Danjovic/TicTacX/doc/boardVersions16F648A.png

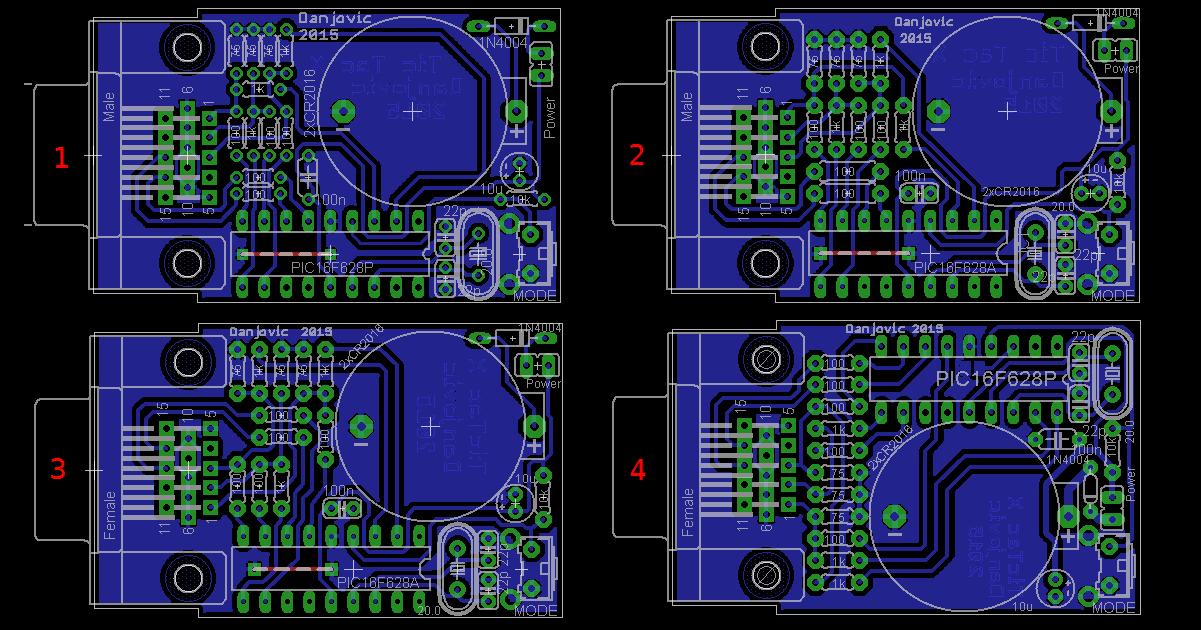
doc/boardVersions16F648A.png
