Danjovic/TicTacX/doc/boardVersions16F688.png

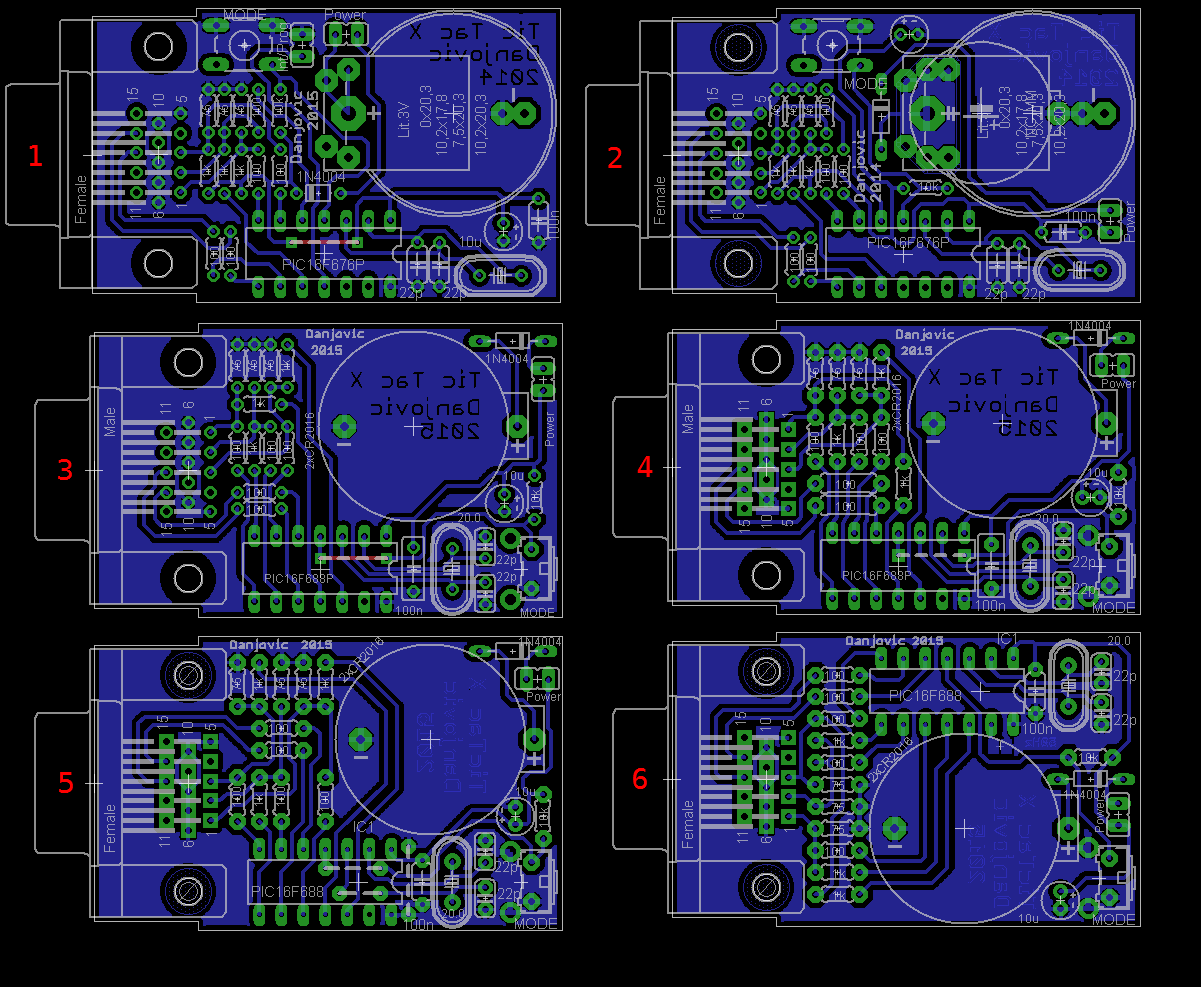
doc/boardVersions16F688.png
