Danjovic/TicTacX/doc/modos.png

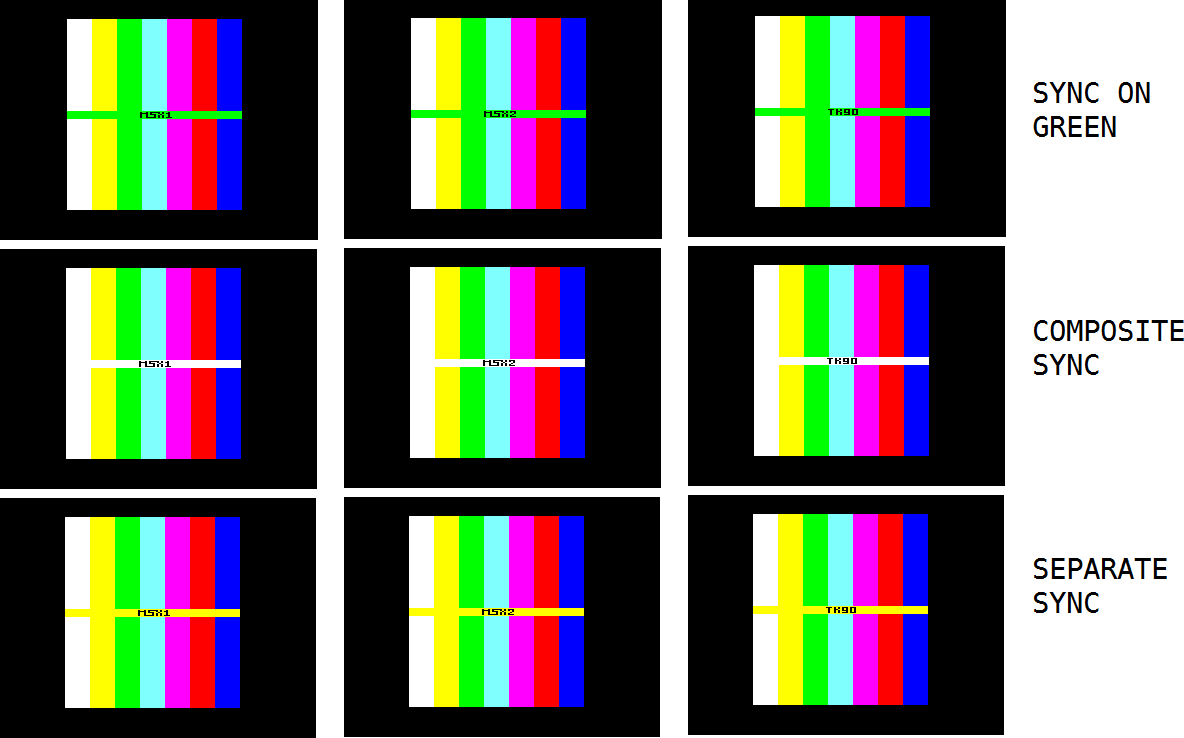
doc/modos.png
