Danjovic/TicTacX/doc/NEC-EA192M/DSC_2613.jpg

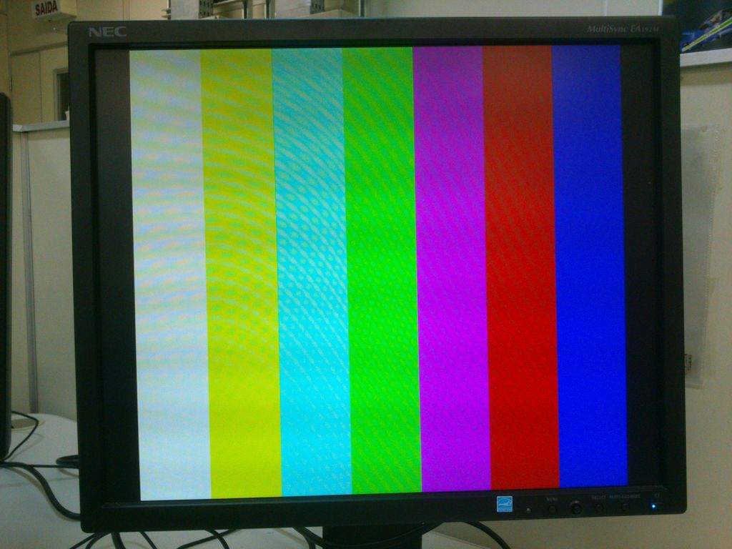
doc/NEC-EA192M/DSC_2613.jpg
