Danjovic/TicTacX/doc/NEC-EA192M/DSC_2616.jpg

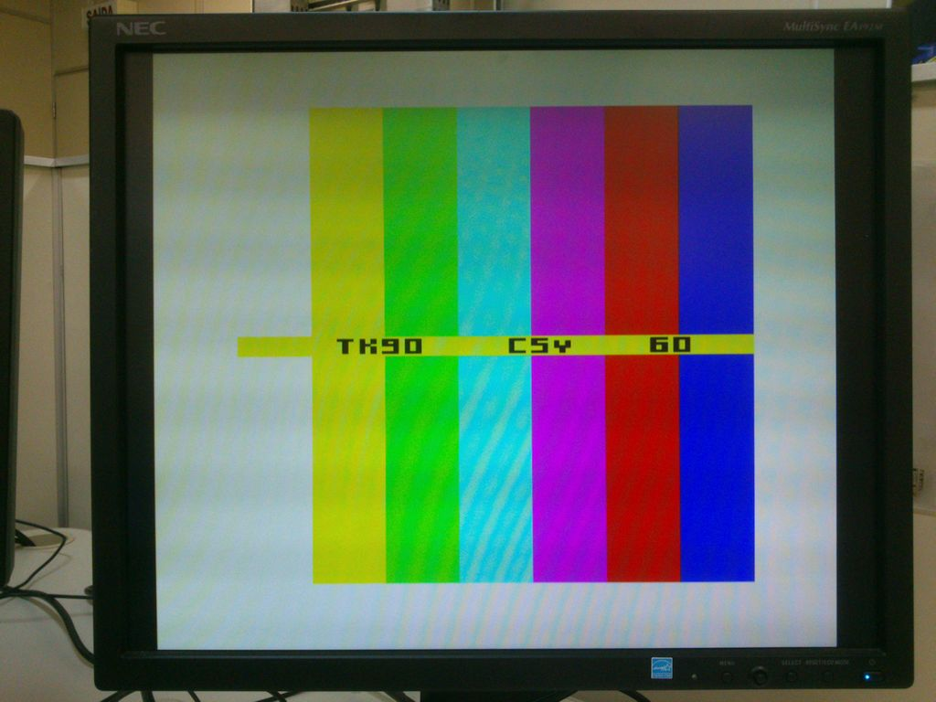
doc/NEC-EA192M/DSC_2616.jpg
