Danjovic/TicTacX/doc/NEC-EA192M/DSC_2620.jpg

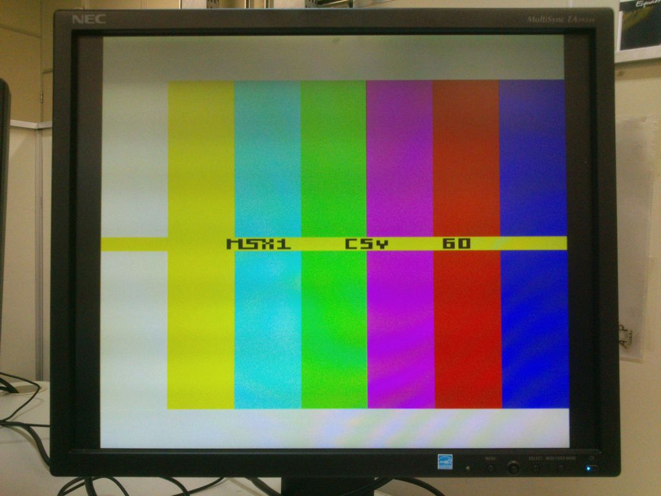
doc/NEC-EA192M/DSC_2620.jpg
