Danjovic/TicTacX/doc/NEC-EA192M/DSC_2622.jpg

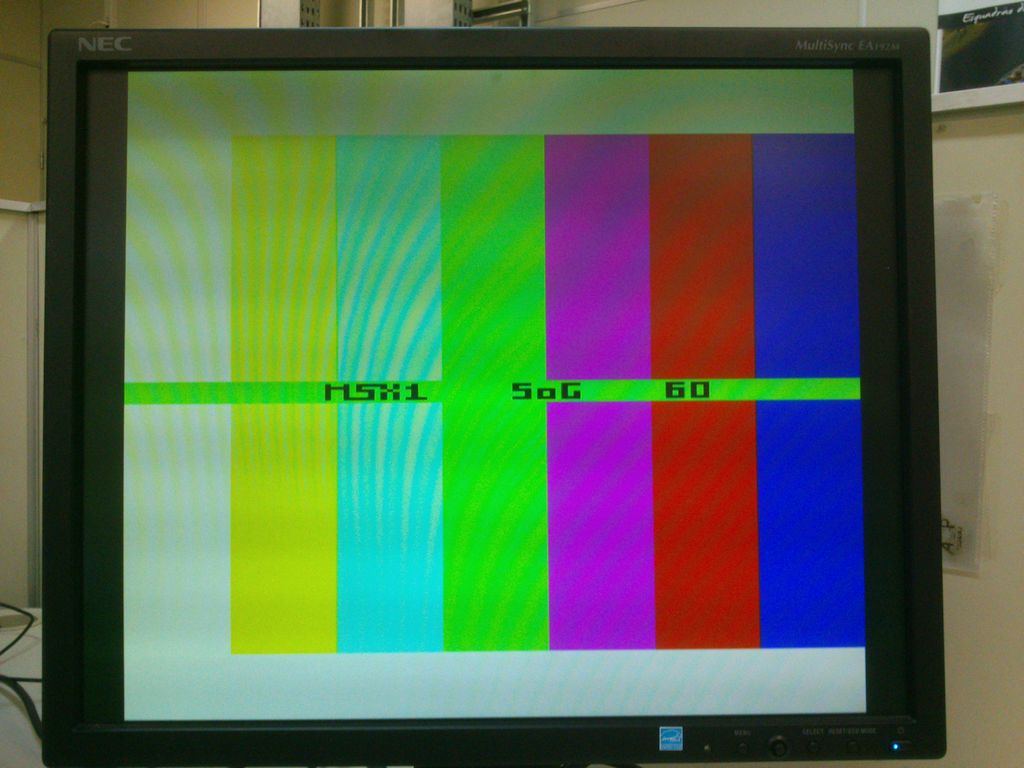
doc/NEC-EA192M/DSC_2622.jpg
