Danjovic/TicTacX/doc/NEC-EA192M/DSC_2623.jpg

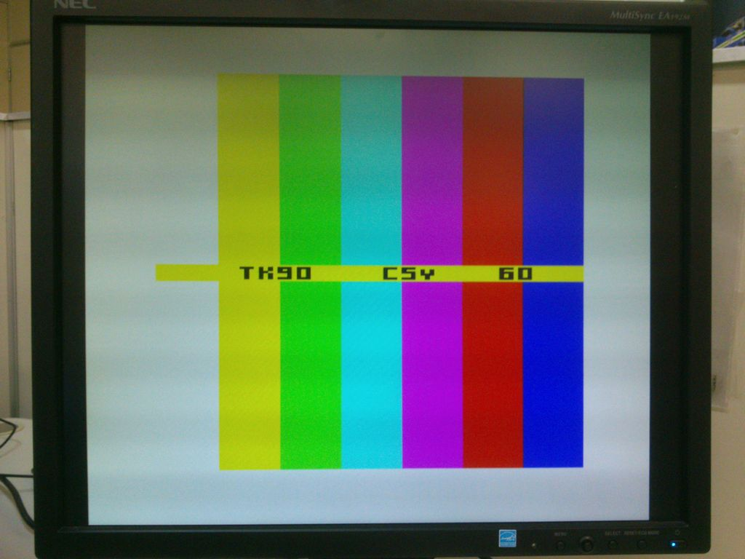
doc/NEC-EA192M/DSC_2623.jpg
