Danjovic/TicTacX/doc/NEC-EA192M/DSC_2625.jpg

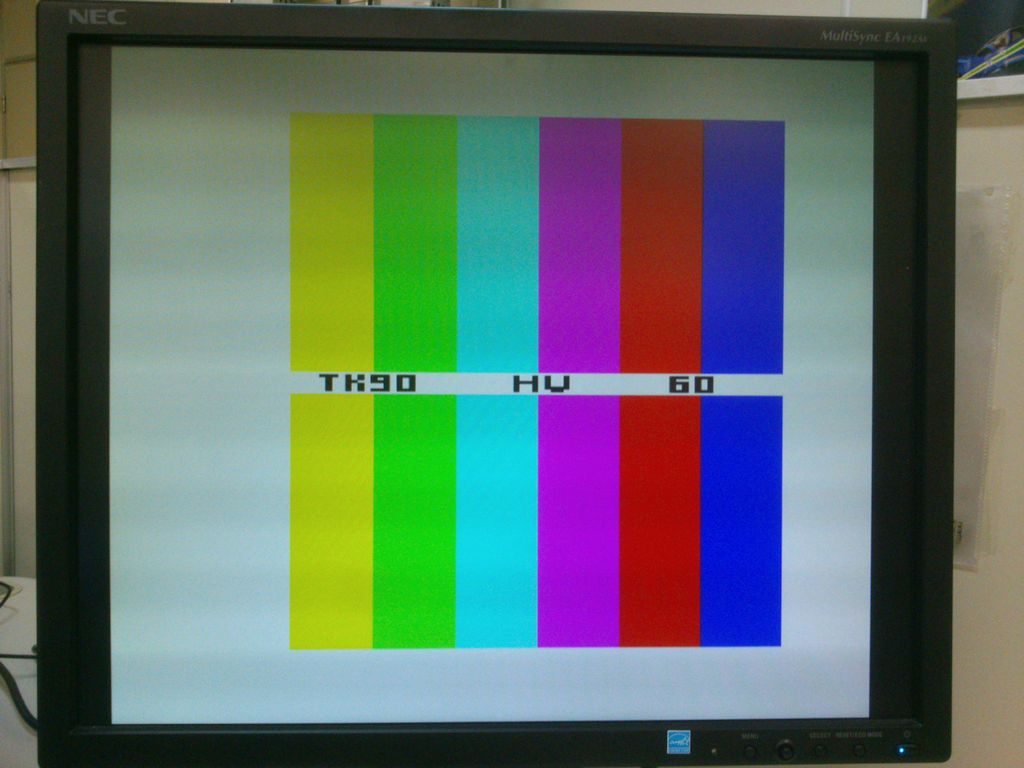
doc/NEC-EA192M/DSC_2625.jpg
