Danjovic/TicTacX/doc/NEC-EA192M/DSC_2626.jpg

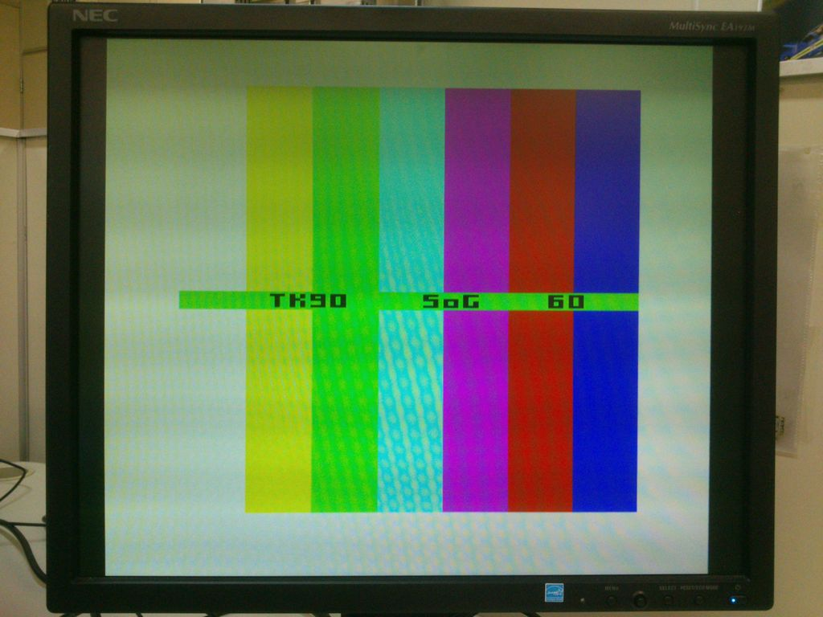
doc/NEC-EA192M/DSC_2626.jpg
