Danjovic/TicTacX/doc/NEC-EA192M/DSC_2627.jpg

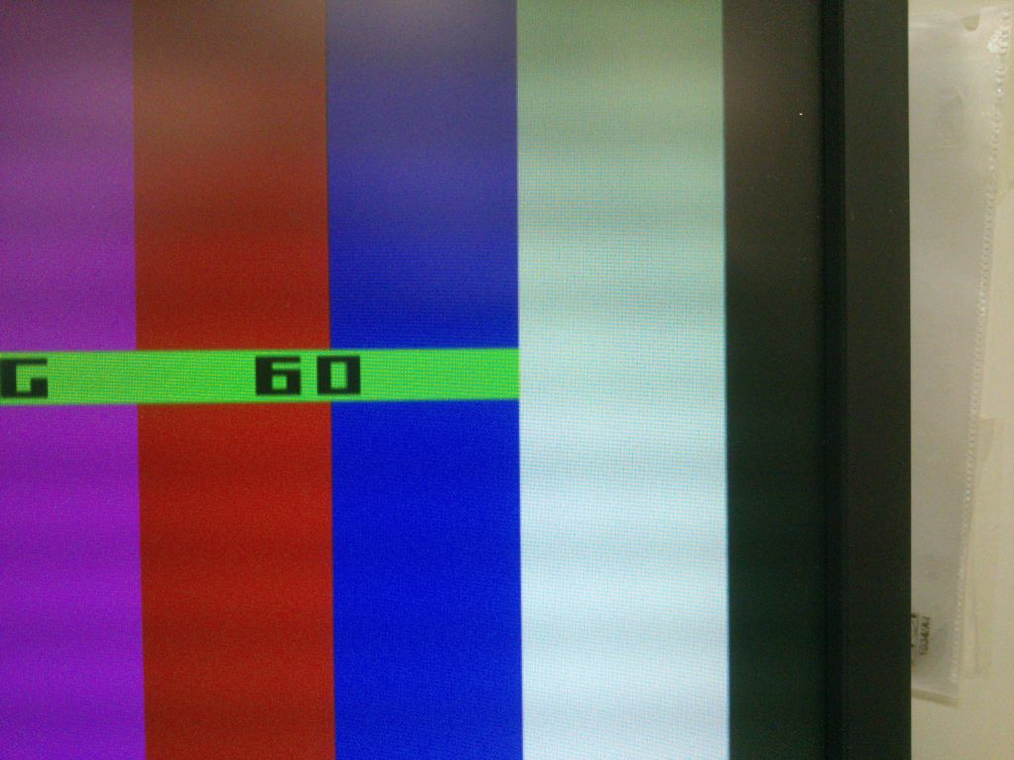
doc/NEC-EA192M/DSC_2627.jpg
