Danjovic/TicTacX/doc/NEC-EA192M/DSC_2628.jpg

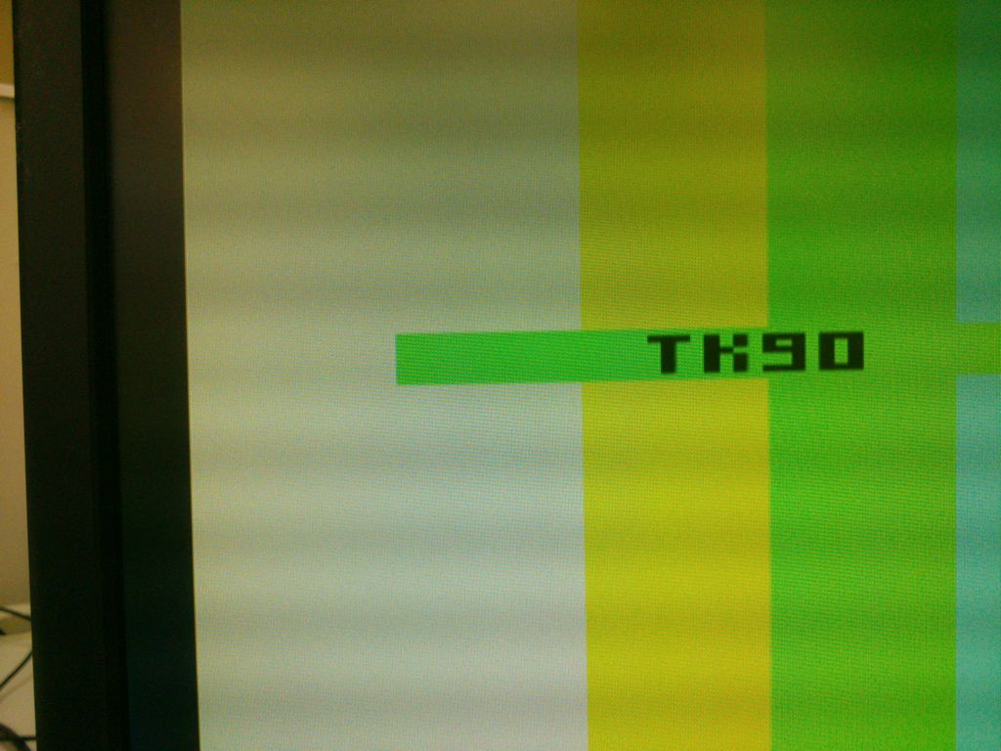
doc/NEC-EA192M/DSC_2628.jpg
