Danjovic/TicTacX/doc/NEC-EA192M/DSC_2629.jpg

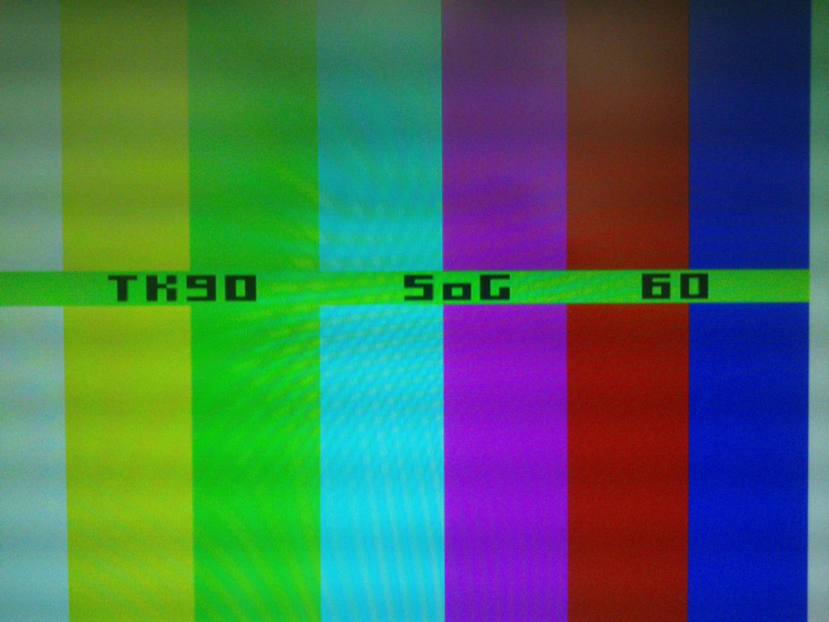
doc/NEC-EA192M/DSC_2629.jpg
