Danjovic/TicTacX/doc/NEC-EA192M/DSC_2630.jpg

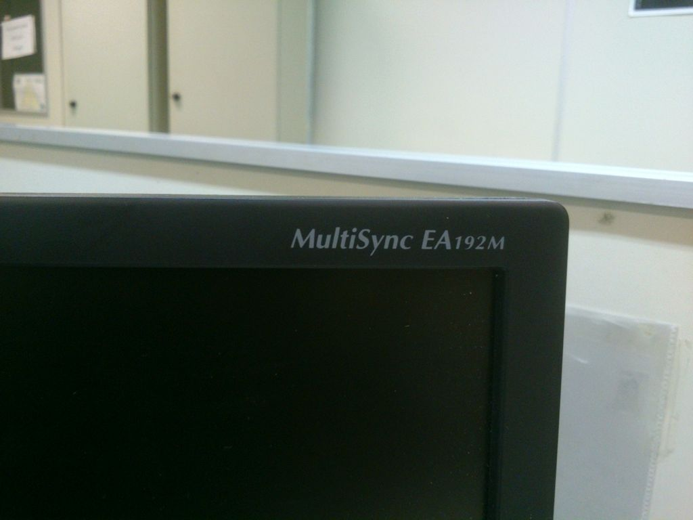
doc/NEC-EA192M/DSC_2630.jpg
