Danjovic/TicTacX/doc/pixels no excel.png

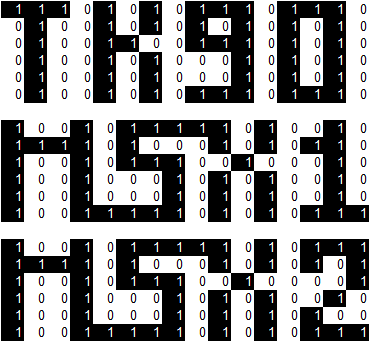
doc/pixels no excel.png
