Danjovic/TicTacX/doc/Renderizacoes2.PNG

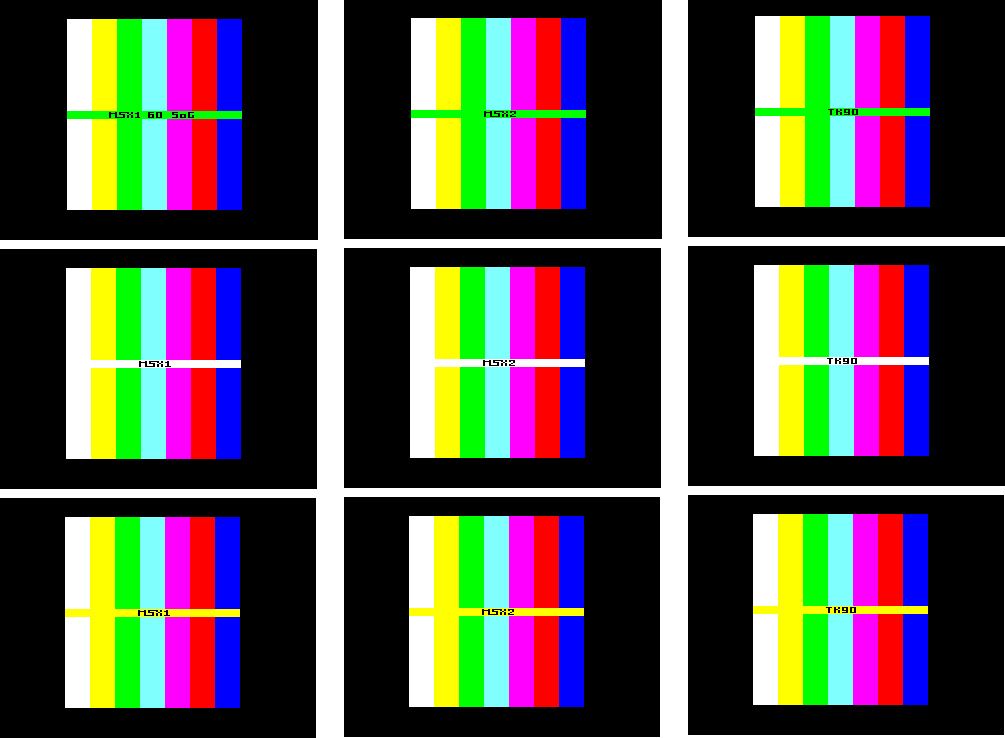
doc/Renderizacoes2.PNG
