Danjovic/TicTacX/doc/SAMSUNG-510N/DSC_2728.jpg

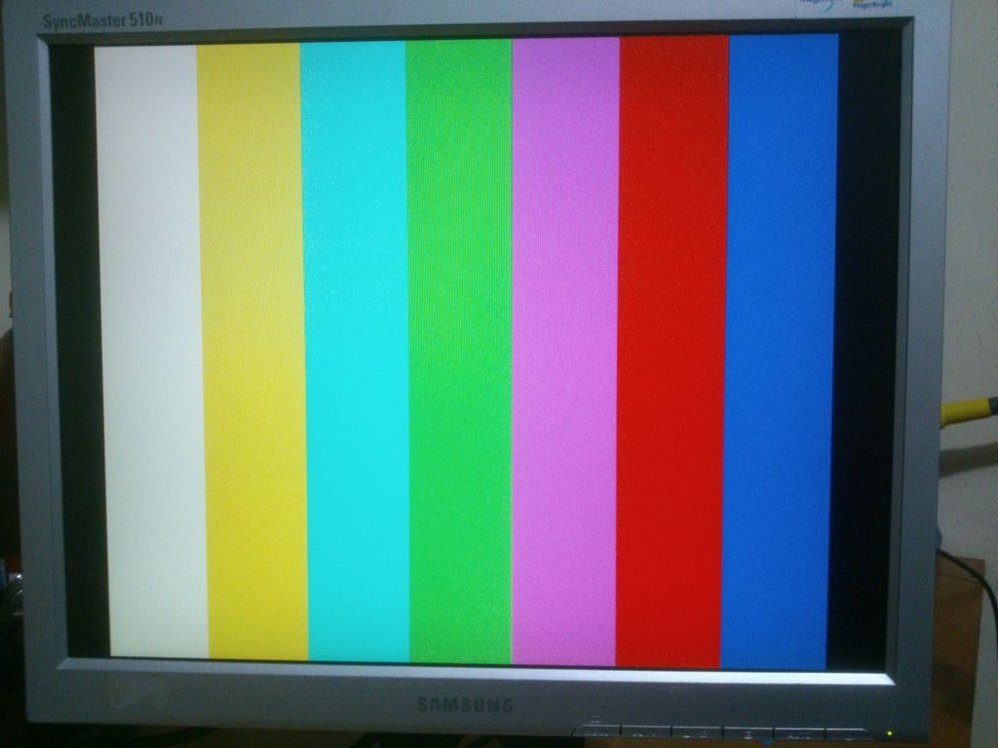
doc/SAMSUNG-510N/DSC_2728.jpg
