Danjovic/TicTacX/doc/SAMSUNG-510N/DSC_2729.jpg

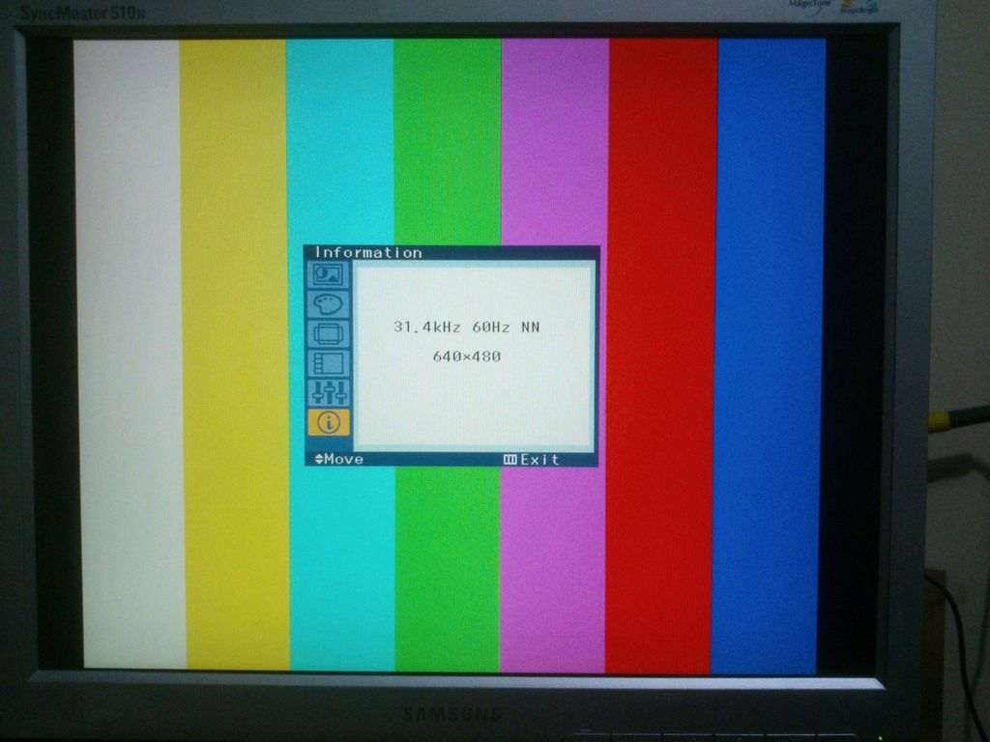
doc/SAMSUNG-510N/DSC_2729.jpg
