Danjovic/TicTacX/doc/SAMSUNG-510N/DSC_2730.jpg

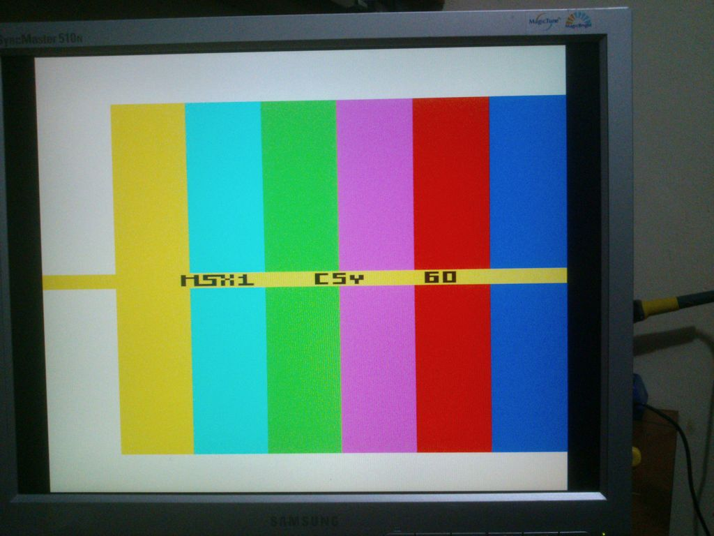
doc/SAMSUNG-510N/DSC_2730.jpg
