Danjovic/TicTacX/doc/SAMSUNG-510N/DSC_2731.jpg

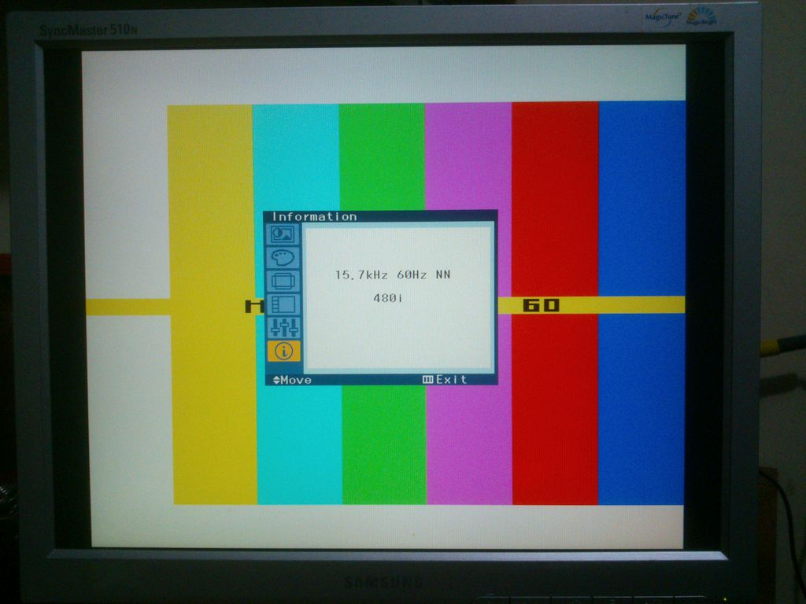
doc/SAMSUNG-510N/DSC_2731.jpg
