Danjovic/TicTacX/doc/SAMSUNG-510N/DSC_2733.jpg

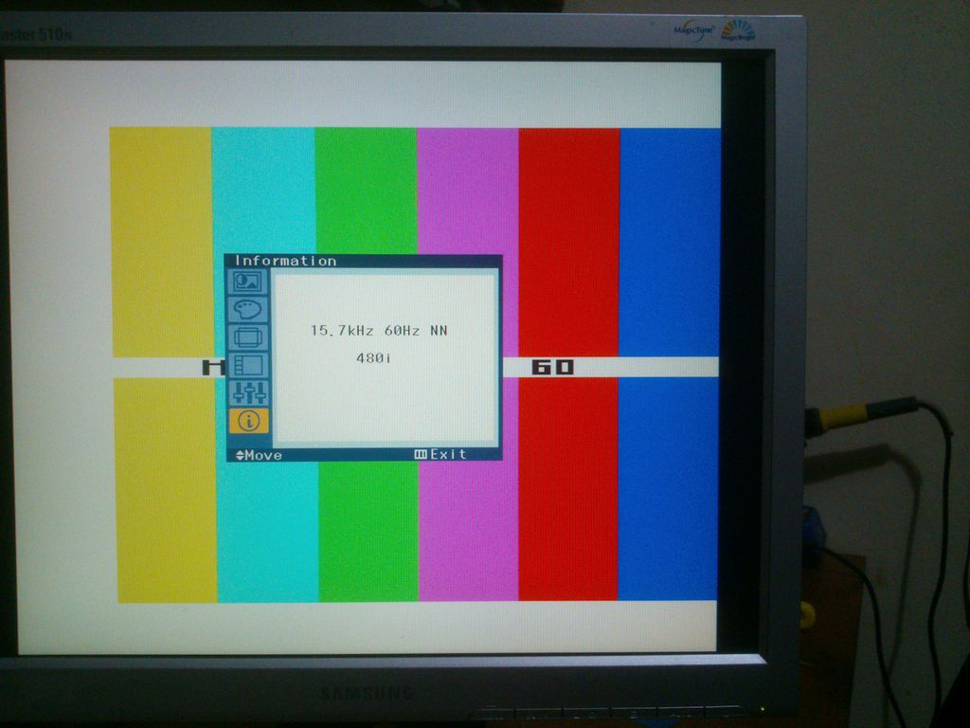
doc/SAMSUNG-510N/DSC_2733.jpg
