Danjovic/TicTacX/doc/SAMSUNG-510N/DSC_2734.jpg

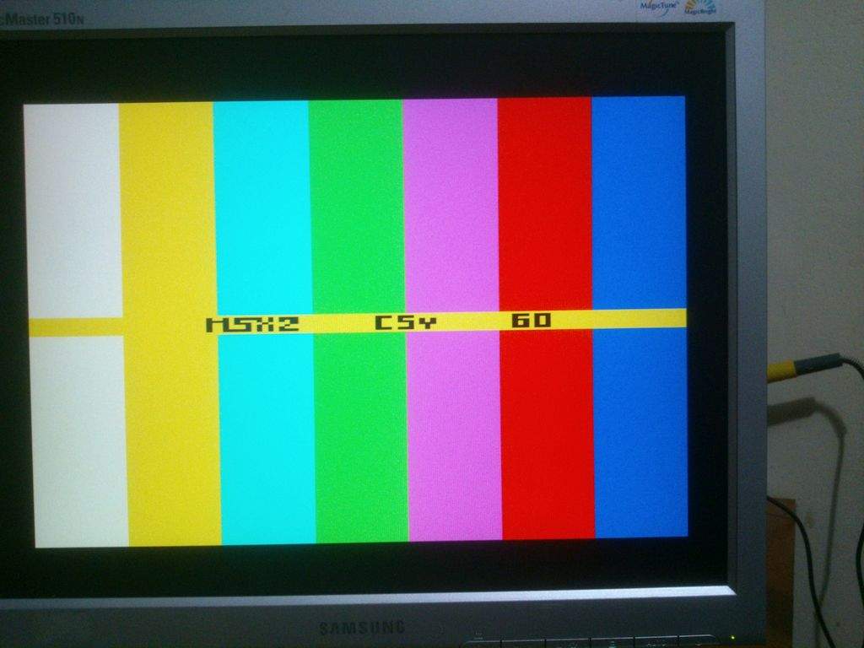
doc/SAMSUNG-510N/DSC_2734.jpg
