Danjovic/TicTacX/doc/SAMSUNG-510N/DSC_2735.jpg

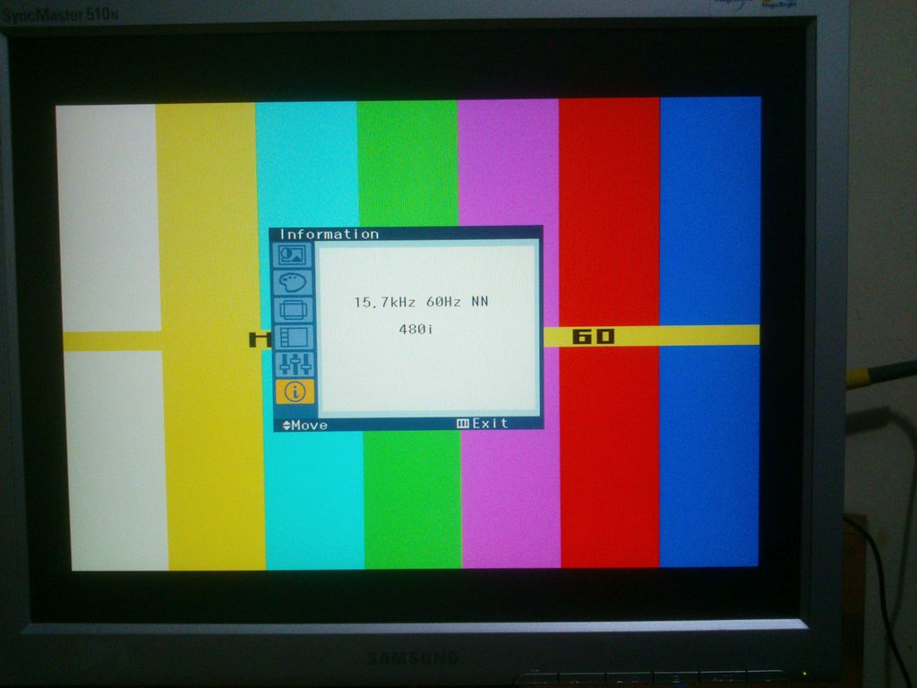
doc/SAMSUNG-510N/DSC_2735.jpg
