Danjovic/TicTacX/doc/SAMSUNG-510N/DSC_2736.jpg

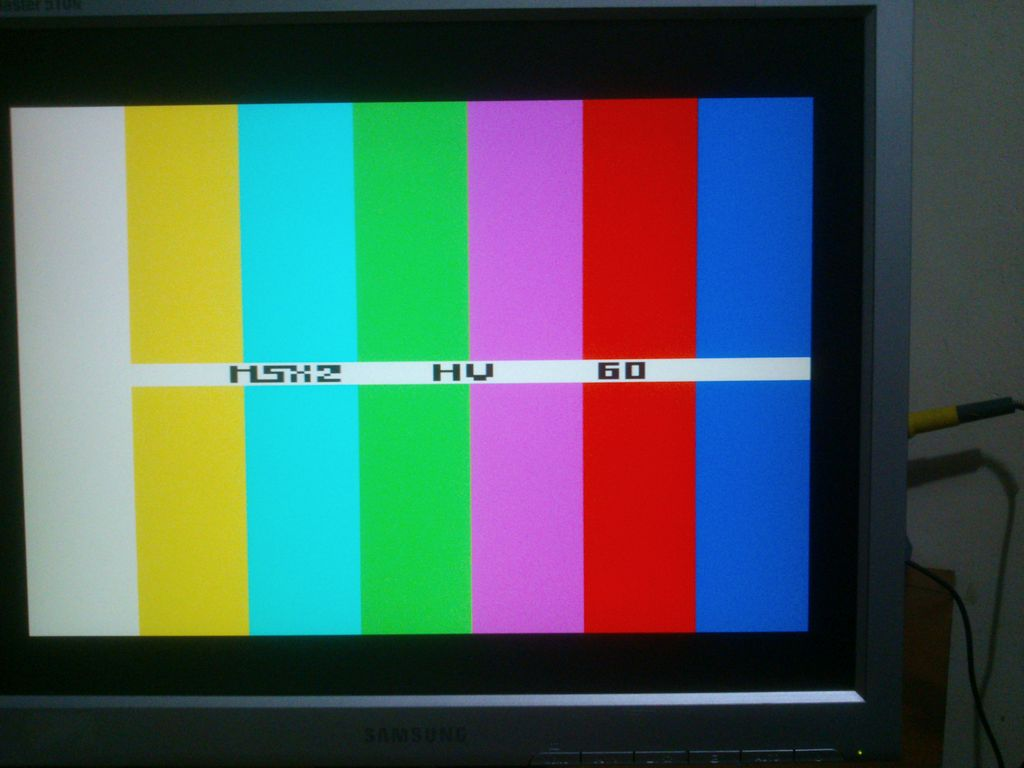
doc/SAMSUNG-510N/DSC_2736.jpg
