Danjovic/TicTacX/doc/SAMSUNG-510N/DSC_2737.jpg

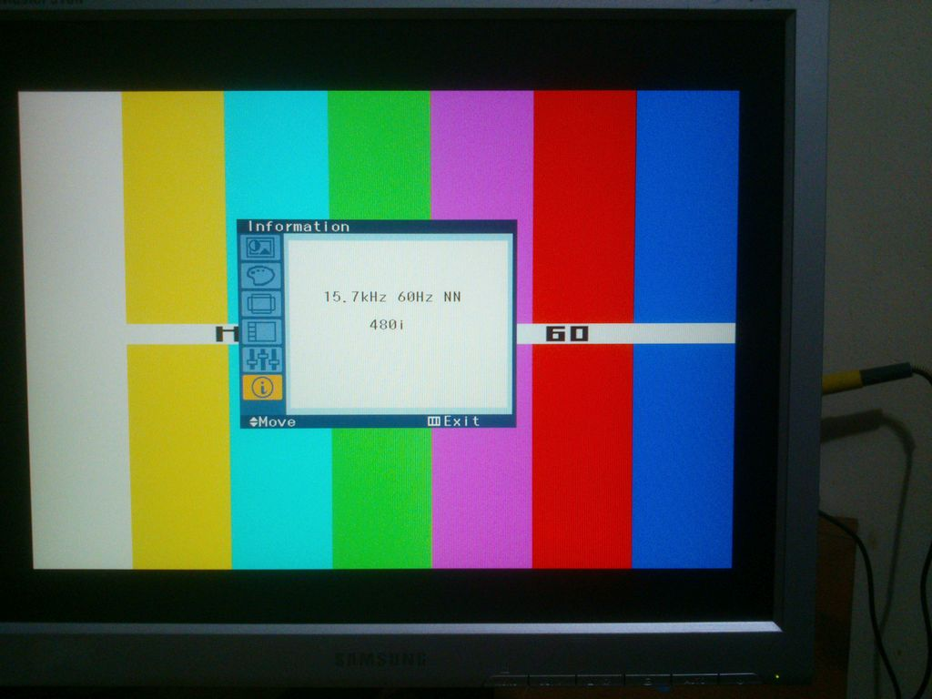
doc/SAMSUNG-510N/DSC_2737.jpg
