Danjovic/TicTacX/doc/SAMSUNG-510N/DSC_2738.jpg

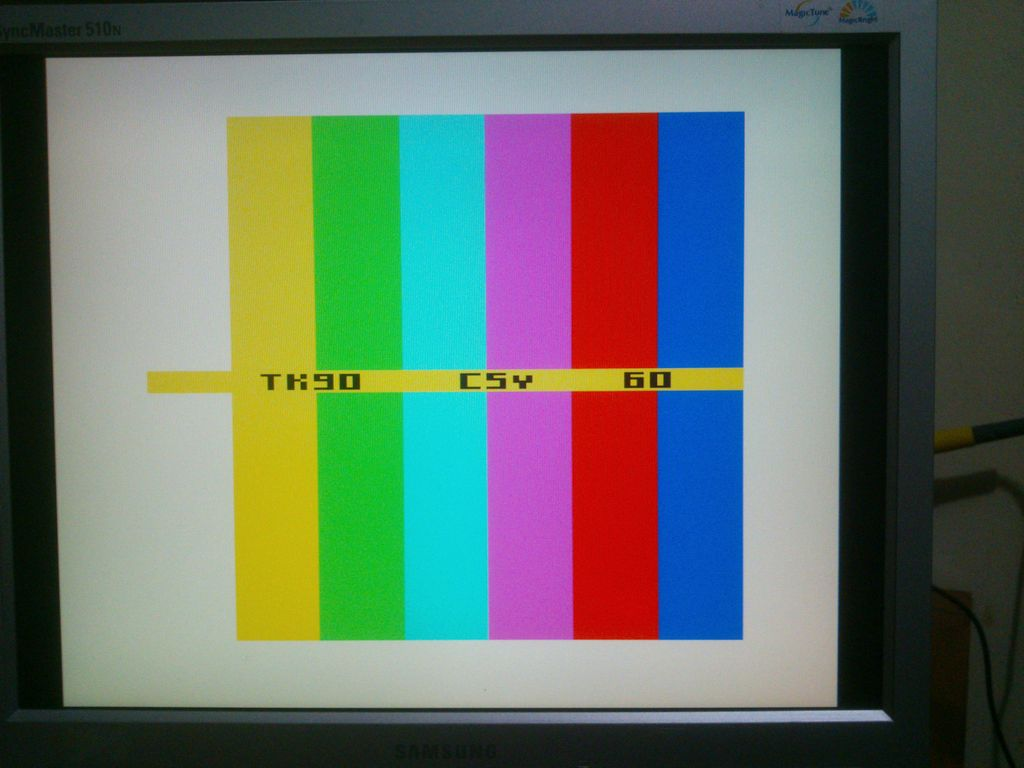
doc/SAMSUNG-510N/DSC_2738.jpg
