Danjovic/TicTacX/doc/SAMSUNG-510N/DSC_2739.jpg

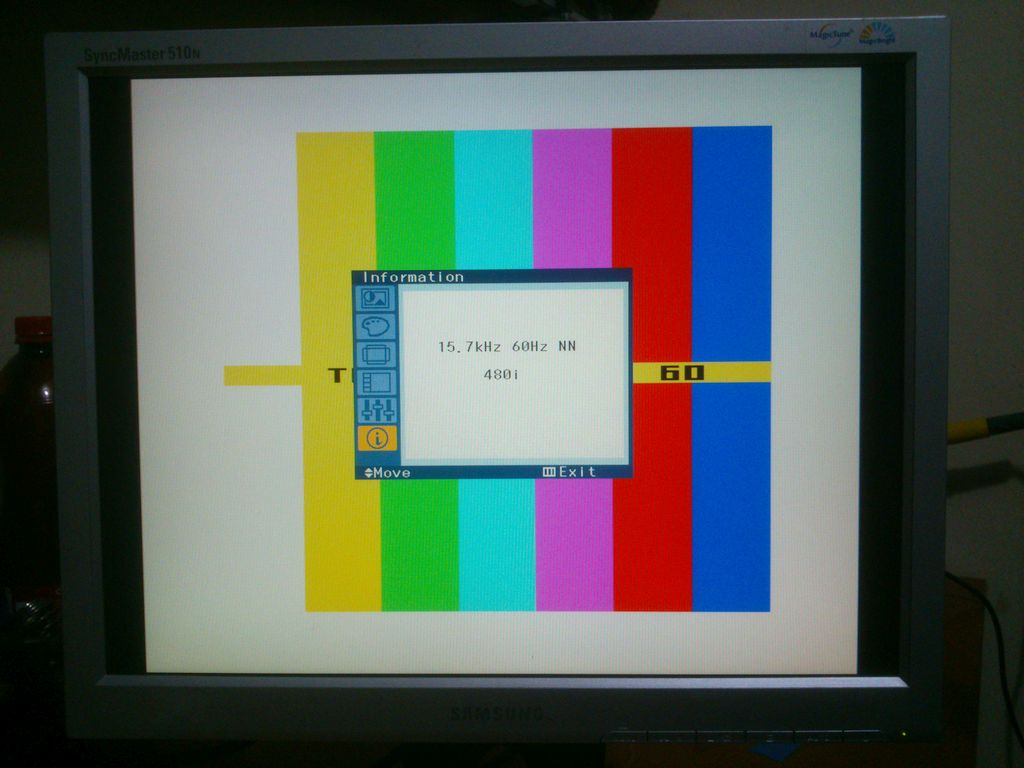
doc/SAMSUNG-510N/DSC_2739.jpg
