Danjovic/TicTacX/doc/SAMSUNG-510N/DSC_2740.jpg

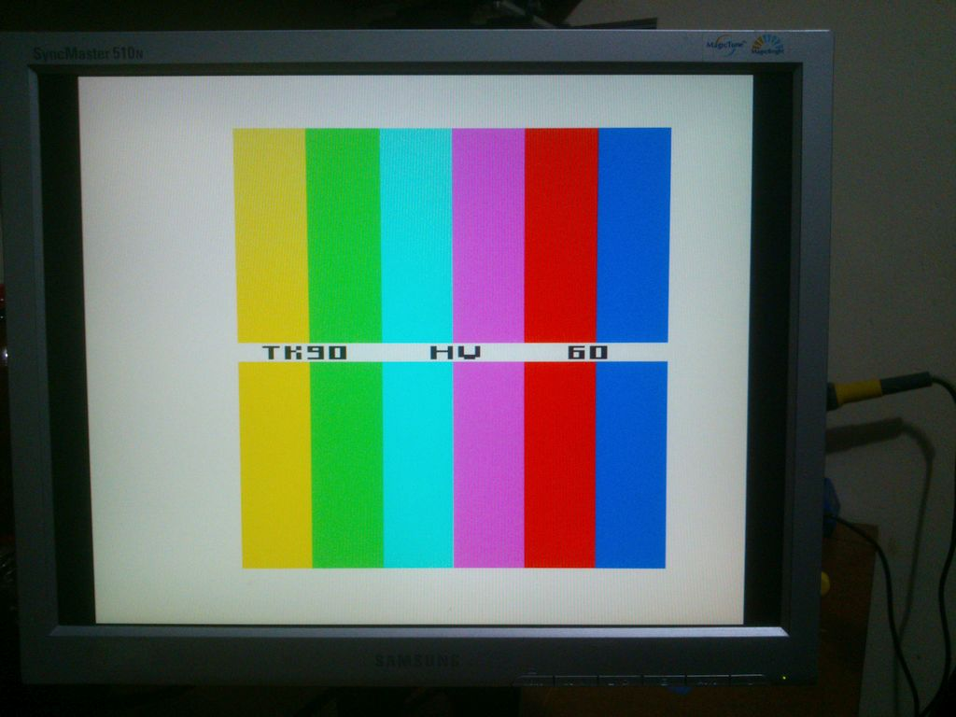
doc/SAMSUNG-510N/DSC_2740.jpg
