Danjovic/TicTacX/doc/SAMSUNG-510N/DSC_2741.jpg

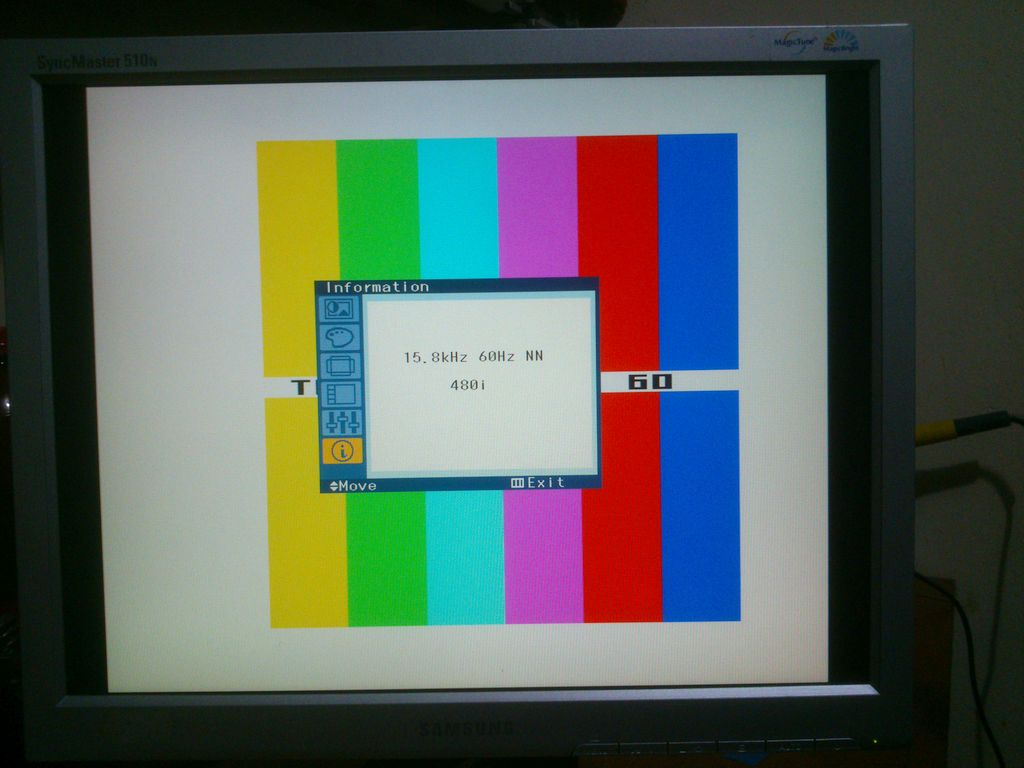
doc/SAMSUNG-510N/DSC_2741.jpg
