Danjovic/TicTacX/doc/SAMSUNG-510N/DSC_2742.jpg

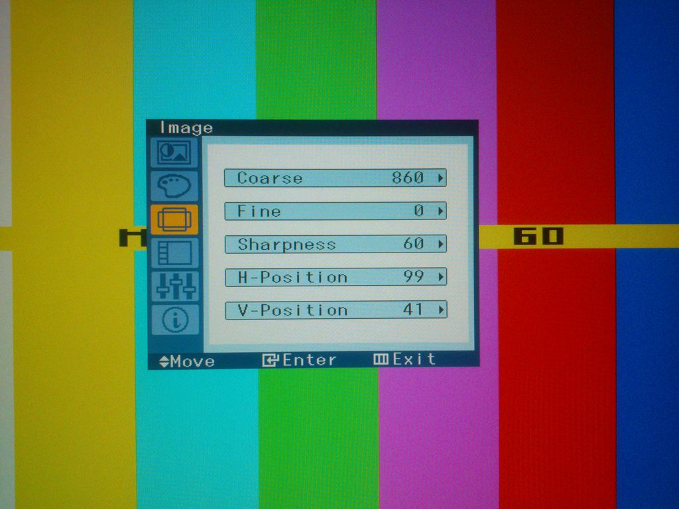
doc/SAMSUNG-510N/DSC_2742.jpg
