Danjovic/TicTacX/doc/Selecting16F648.png

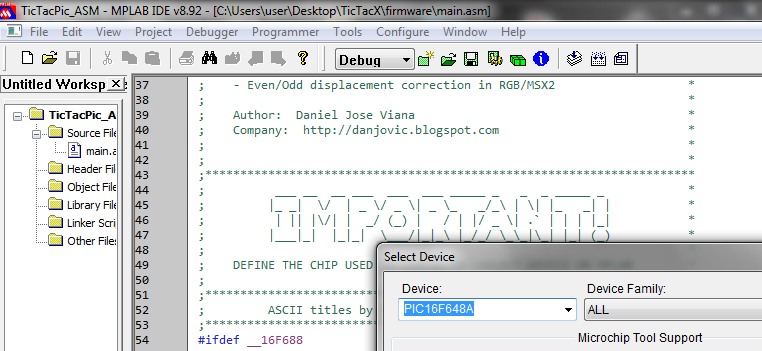
doc/Selecting16F648.png
