Danjovic/TicTacX/doc/Waveforms/MSX/MSX1 Vser real vs gerado.png

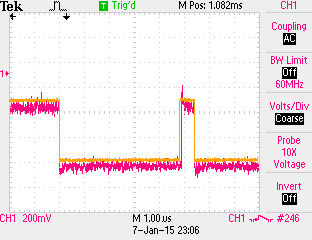
doc/Waveforms/MSX/MSX1 Vser real vs gerado.png
