Danjovic/TicTacX/doc/Waveforms/MSX/MSX Inicio do Vsync.png

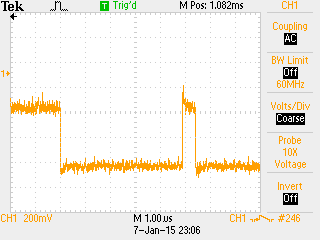
doc/Waveforms/MSX/MSX Inicio do Vsync.png
