Danjovic/TicTacX/doc/Waveforms/MSX/MSX Linha de video.png

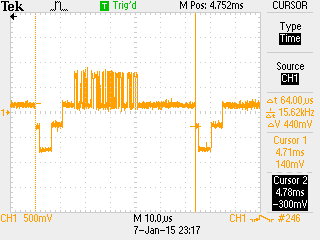
doc/Waveforms/MSX/MSX Linha de video.png
