Danjovic/TicTacX/doc/Waveforms/MSX/MSX Y-PB-PR niveis.png

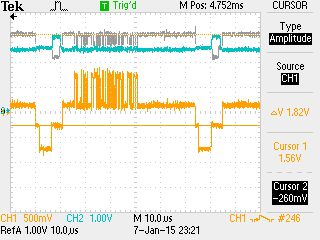
doc/Waveforms/MSX/MSX Y-PB-PR niveis.png
