Danjovic/TicTacX/doc/Waveforms/MSX/Sincronismo.png

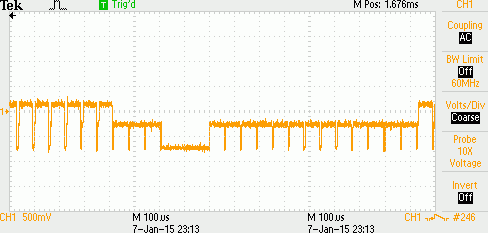
doc/Waveforms/MSX/Sincronismo.png
