Danjovic/TicTacX/doc/Waveforms/MSX/TEK0030.TIF

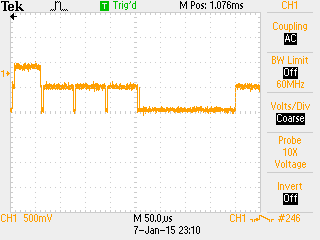
doc/Waveforms/MSX/TEK0030.TIF
