Danjovic/TicTacX/doc/Waveforms/MSX/TEK0031.TIF

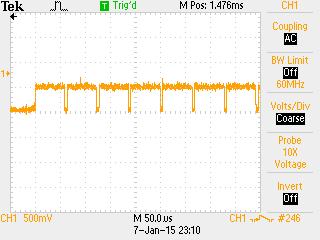
doc/Waveforms/MSX/TEK0031.TIF
