Danjovic/TicTacX/doc/Waveforms/MSX/TEK0034.TIF

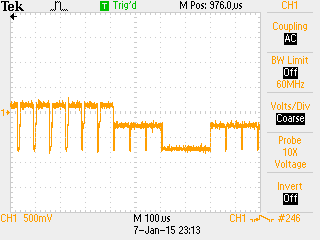
doc/Waveforms/MSX/TEK0034.TIF
