Danjovic/TicTacX/doc/Waveforms/MSX/TEK0035.TIF

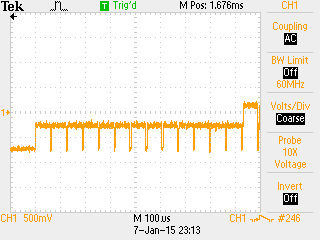
doc/Waveforms/MSX/TEK0035.TIF
