Danjovic/TicTacX/doc/Waveforms/MSX/TEK0036.TIF

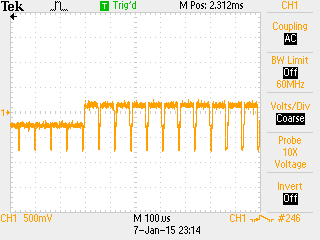
doc/Waveforms/MSX/TEK0036.TIF
