Danjovic/TicTacX/doc/Waveforms/MSX/TEK0037.TIF

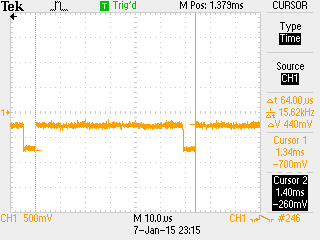
doc/Waveforms/MSX/TEK0037.TIF
