Danjovic/TicTacX/doc/Waveforms/MSX/TEK0038.TIF

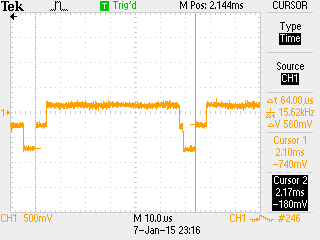
doc/Waveforms/MSX/TEK0038.TIF
