Danjovic/TicTacX/doc/Waveforms/MSX/TEK0040.TIF

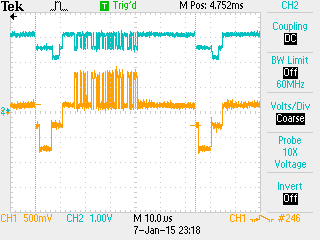
doc/Waveforms/MSX/TEK0040.TIF
