Danjovic/TicTacX/doc/Waveforms/MSX/TEK0041.TIF

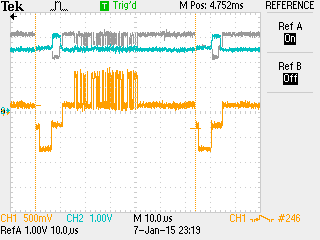
doc/Waveforms/MSX/TEK0041.TIF
