Danjovic/TicTacX/doc/Waveforms/Sinais de sincronismo.png

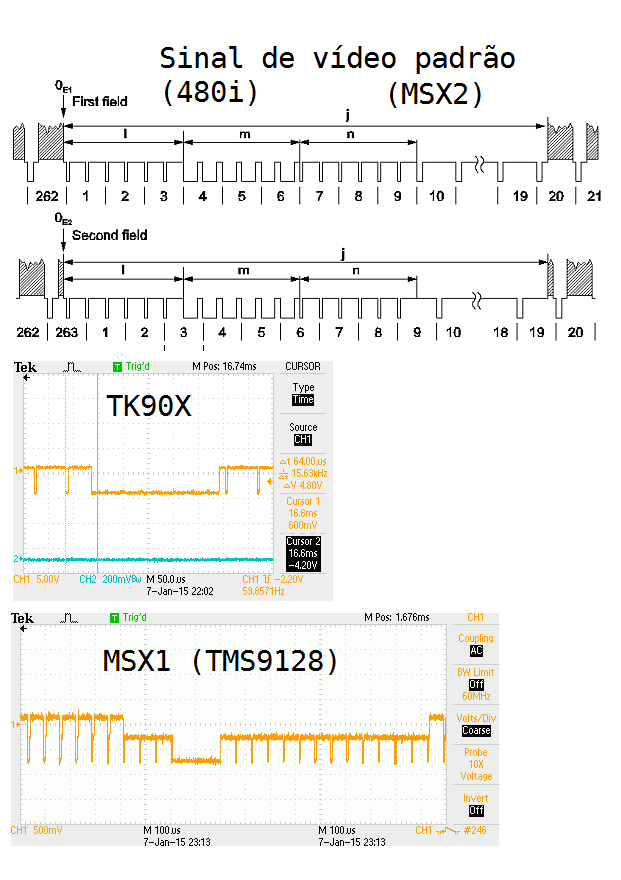
doc/Waveforms/Sinais de sincronismo.png
