Danjovic/TicTacX/doc/Waveforms/TK90X/TEK0014.TIF

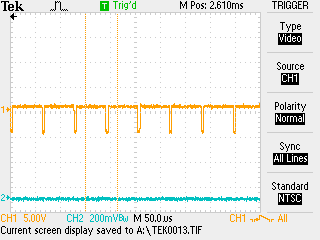
doc/Waveforms/TK90X/TEK0014.TIF
