Danjovic/TicTacX/doc/Waveforms/TK90X/TEK0015.TIF

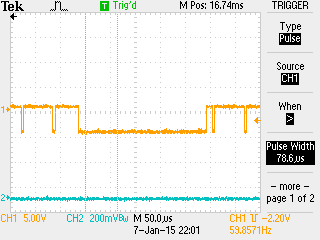
doc/Waveforms/TK90X/TEK0015.TIF
