Danjovic/TicTacX/doc/Waveforms/TK90X/TEK0016.TIF

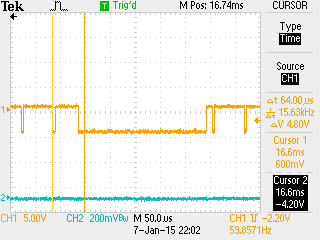
doc/Waveforms/TK90X/TEK0016.TIF
