Danjovic/TicTacX/doc/Waveforms/TK90X/TEK0017.TIF

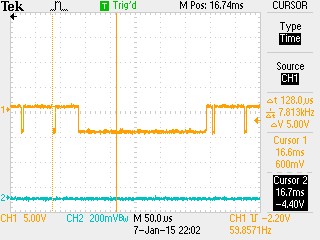
doc/Waveforms/TK90X/TEK0017.TIF
