Danjovic/TicTacX/doc/Waveforms/TK90X/TEK0018.TIF

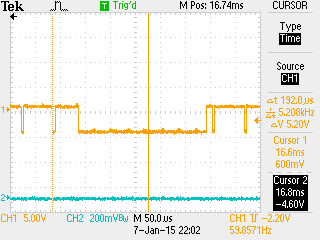
doc/Waveforms/TK90X/TEK0018.TIF
