Danjovic/TicTacX/doc/Waveforms/TK90X/TEK0019.TIF

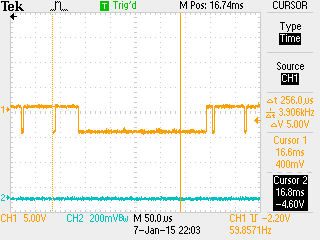
doc/Waveforms/TK90X/TEK0019.TIF
