Danjovic/TicTacX/doc/Waveforms/TK90X/TEK0021.TIF

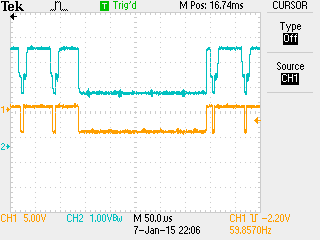
doc/Waveforms/TK90X/TEK0021.TIF
