Danjovic/TicTacX/doc/Waveforms/TK90X/TEK0022.TIF

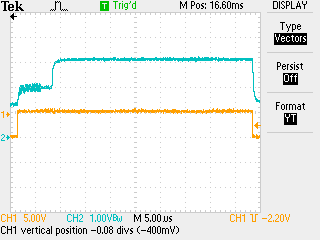
doc/Waveforms/TK90X/TEK0022.TIF
