Danjovic/TicTacX/doc/Waveforms/TK90X/TEK0023.TIF

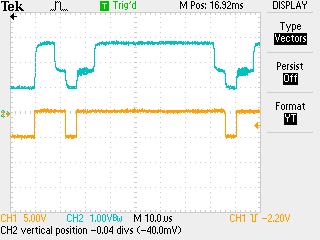
doc/Waveforms/TK90X/TEK0023.TIF
