Danjovic/TicTacX/doc/Waveforms/TK90X/TEK0024.TIF

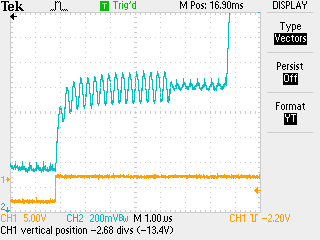
doc/Waveforms/TK90X/TEK0024.TIF
