Danjovic/TicTacX/doc/Waveforms/TK90X/TEK0025.TIF

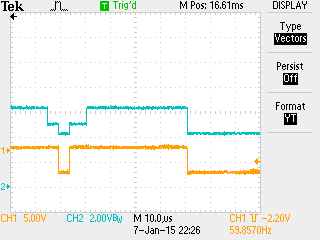
doc/Waveforms/TK90X/TEK0025.TIF
