Danjovic/TicTacX/doc/Waveforms/TK90X/TEK0026.TIF

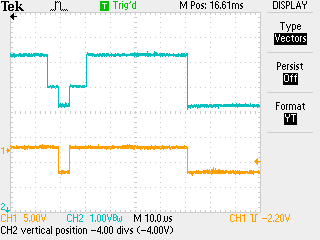
doc/Waveforms/TK90X/TEK0026.TIF
