Danjovic/TicTacX/doc/Waveforms/TK90X/TEK0027.TIF

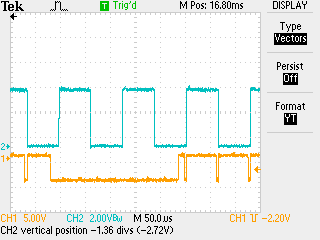
doc/Waveforms/TK90X/TEK0027.TIF
