Danjovic/TicTacX/doc/Waveforms/TK90X/TEK0028.TIF

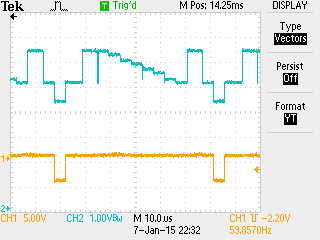
doc/Waveforms/TK90X/TEK0028.TIF
