Danjovic/TicTacX/doc/Waveforms/TK90X/ULA Backporch.png

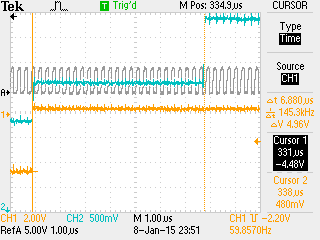
doc/Waveforms/TK90X/ULA Backporch.png
