Danjovic/TicTacX/doc/Waveforms/TK90X/ULA Frontporch.png

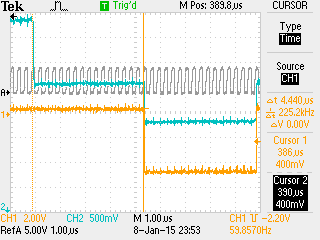
doc/Waveforms/TK90X/ULA Frontporch.png
