Danjovic/TicTacX/doc/Waveforms/TK90X/ULA Heq1.png

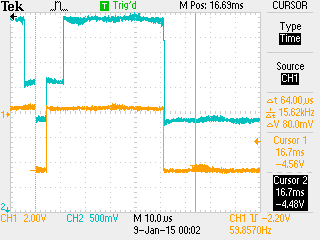
doc/Waveforms/TK90X/ULA Heq1.png
