Danjovic/TicTacX/doc/Waveforms/TK90X/ULA Hsync.png

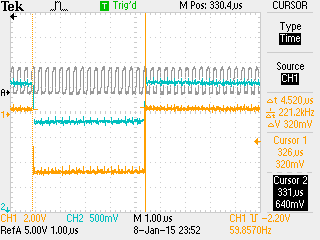
doc/Waveforms/TK90X/ULA Hsync.png
