Danjovic/TicTacX/doc/Waveforms/TK90X/ULA Tline 16_71us.png

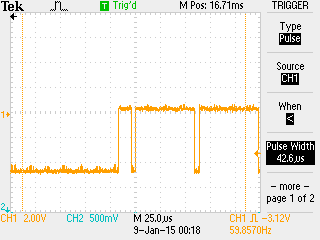
doc/Waveforms/TK90X/ULA Tline 16_71us.png
